CalamityCow/MacOS-Keyboard-Submission/PCB/LED.kicad_sch

## KiCad design PCB/LED.kicad_sch (2025-12-03)

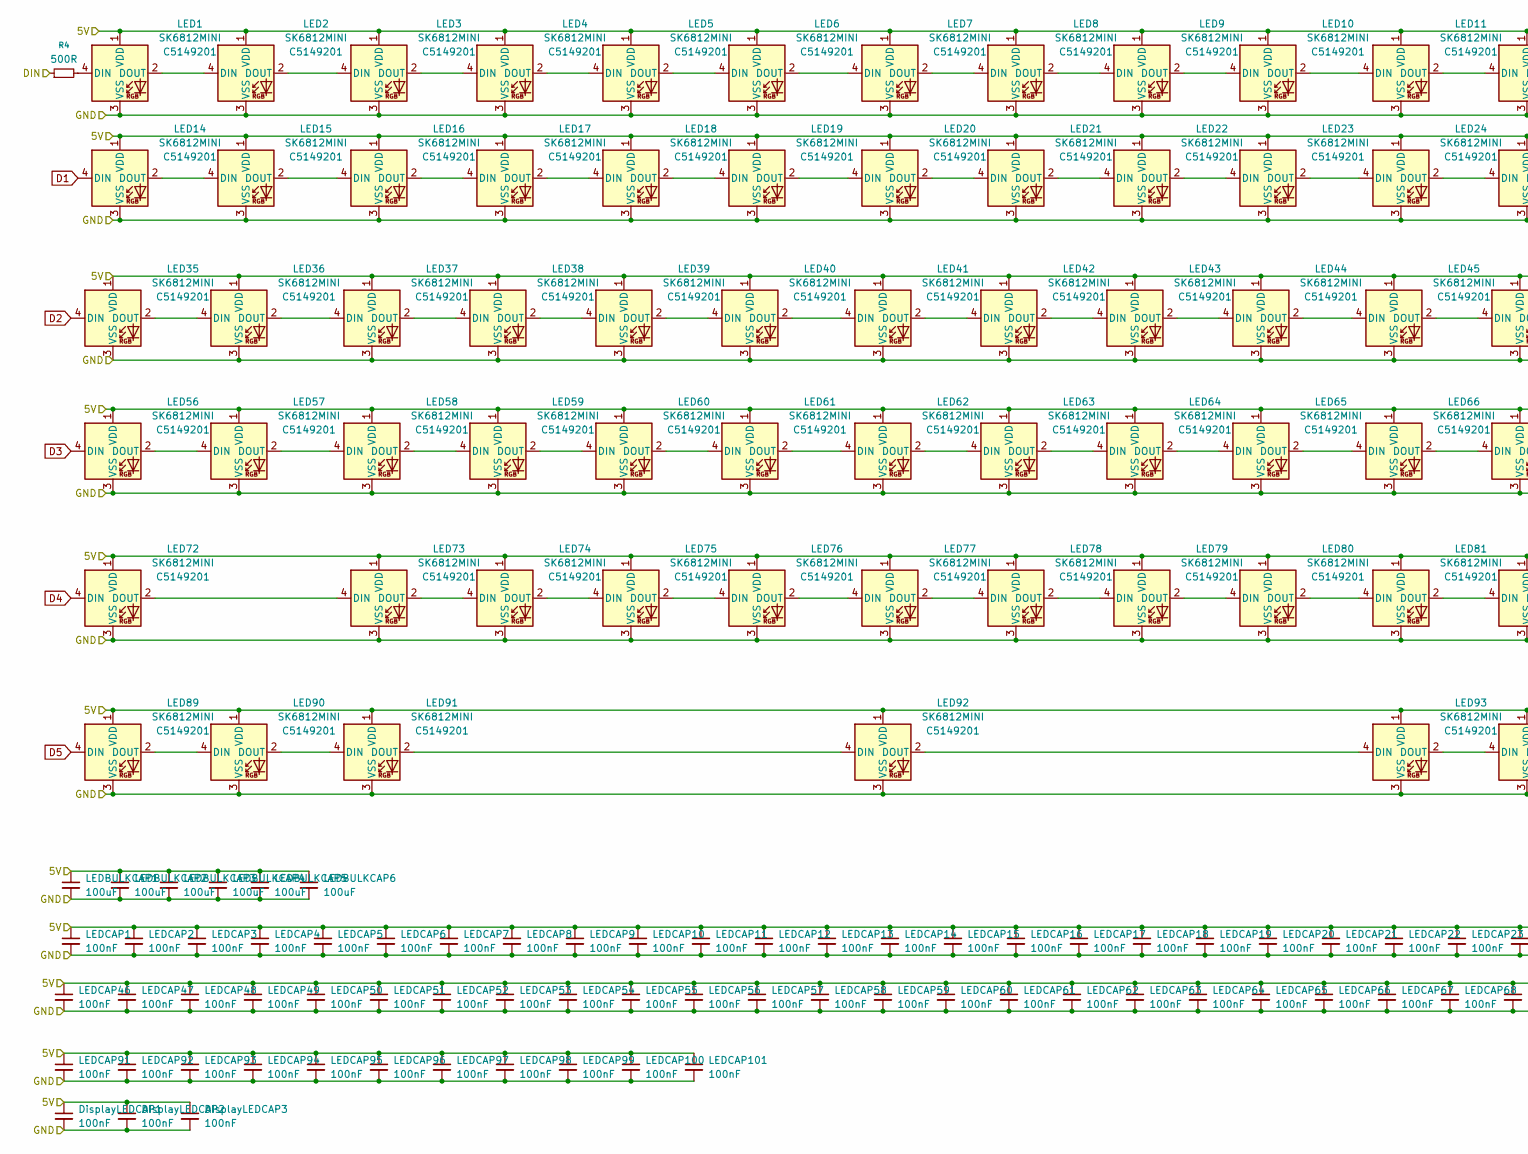
[picture p2: schematic LED.kicad_sch, part in row 1, column 1]

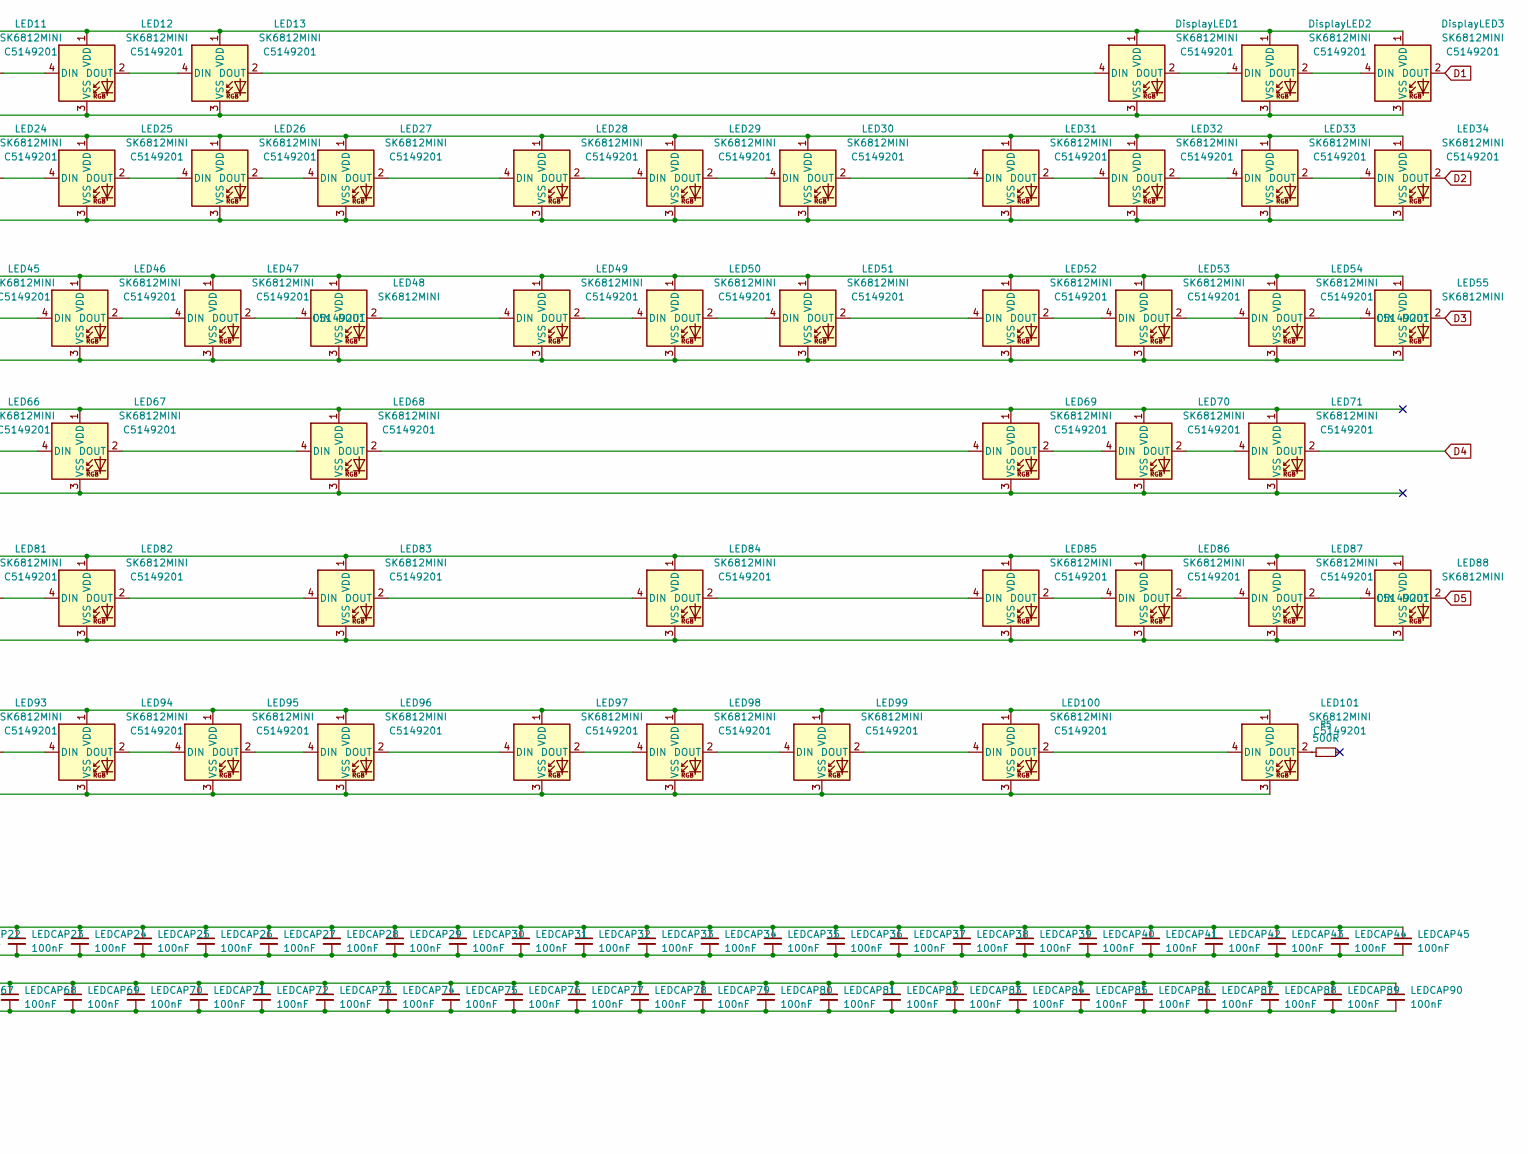
[picture p3: schematic LED.kicad_sch, part in row 1, column 2]

Parts:
DisplayLED1, DisplayLED2, DisplayLED3: SK6812MINI; LED_SK6812MINI; LCSC C5149201
DisplayLEDCAP1, DisplayLEDCAP2, DisplayLEDCAP3: 100nF; Capacitor_0402
LED1, LED2, LED3, LED4, LED5, LED6, LED7, LED8, LED9, LED10, LED11, LED12, LED13, LED14, LED15, LED16, LED17, LED18, LED19, LED20, LED21, LED22, LED23, LED24, LED25, LED26, LED27, LED28, LED29, LED30, LED31, LED32, LED33, LED34, LED35, LED36, LED37, LED38, LED39, LED40, LED41, LED42, LED43, LED44, LED45, LED46, LED47, LED48, LED49, LED50, LED51, LED52, LED53, LED54, LED55, LED56, LED57, LED58, LED59, LED60, LED61, LED62, LED63, LED64, LED65, LED66, LED67, LED68, LED69, LED70, LED71, LED72, LED73, LED74, LED75, LED76, LED77, LED78, LED79, LED80, LED81, LED82, LED83, LED84, LED85, LED86, LED87, LED88, LED89, LED90, LED91, LED92, LED93, LED94, LED95, LED96, LED97, LED98, LED99, LED100, LED101: SK6812MINI; LED_SK6812MINI; LCSC C5149201
LEDBULKCAP1, LEDBULKCAP2, LEDBULKCAP3, LEDBULKCAP4, LEDBULKCAP5, LEDBULKCAP6: 100uF; Capacitor_0402
LEDCAP1, LEDCAP2, LEDCAP3, LEDCAP4, LEDCAP5, LEDCAP6, LEDCAP7, LEDCAP8, LEDCAP9, LEDCAP10, LEDCAP11, LEDCAP12, LEDCAP13, LEDCAP14, LEDCAP15, LEDCAP16, LEDCAP17, LEDCAP18, LEDCAP19, LEDCAP20, LEDCAP21, LEDCAP22, LEDCAP23, LEDCAP24, LEDCAP25, LEDCAP26, LEDCAP27, LEDCAP28, LEDCAP29, LEDCAP30, LEDCAP31, LEDCAP32, LEDCAP33, LEDCAP34, LEDCAP35, LEDCAP36, LEDCAP37, LEDCAP38, LEDCAP39, LEDCAP40, LEDCAP41, LEDCAP42, LEDCAP43, LEDCAP44, LEDCAP45, LEDCAP46, LEDCAP47, LEDCAP48, LEDCAP49, LEDCAP50, LEDCAP51, LEDCAP52, LEDCAP53, LEDCAP54, LEDCAP55, LEDCAP56, LEDCAP57, LEDCAP58, LEDCAP59, LEDCAP60, LEDCAP61, LEDCAP62, LEDCAP63, LEDCAP64, LEDCAP65, LEDCAP66, LEDCAP67, LEDCAP68, LEDCAP69, LEDCAP70, LEDCAP71, LEDCAP72, LEDCAP73, LEDCAP74, LEDCAP75, LEDCAP76, LEDCAP77, LEDCAP78, LEDCAP79, LEDCAP80, LEDCAP81, LEDCAP82, LEDCAP83, LEDCAP84, LEDCAP85, LEDCAP86, LEDCAP87, LEDCAP88, LEDCAP89, LEDCAP90, LEDCAP91, LEDCAP92, LEDCAP93, LEDCAP94, LEDCAP95, LEDCAP96, LEDCAP97, LEDCAP98, LEDCAP99, LEDCAP100, LEDCAP101: 100nF; Capacitor_0402
R4, R5: 500R; Resistor_0402

Connections:
5V: DisplayLED1.1 (VDD), DisplayLED2.1 (VDD), DisplayLED3.1 (VDD), DisplayLEDCAP1.1, DisplayLEDCAP2.1, DisplayLEDCAP3.1, LED1.1 (VDD), LED2.1 (VDD), LED3.1 (VDD), LED4.1 (VDD), LED5.1 (VDD), LED6.1 (VDD), LED7.1 (VDD), LED8.1 (VDD), LED9.1 (VDD), LED10.1 (VDD), LED11.1 (VDD), LED12.1 (VDD), LED13.1 (VDD), LED14.1 (VDD), LED15.1 (VDD), LED16.1 (VDD), LED17.1 (VDD), LED18.1 (VDD), LED19.1 (VDD), LED20.1 (VDD), LED21.1 (VDD), LED22.1 (VDD), LED23.1 (VDD), LED24.1 (VDD), LED25.1 (VDD), LED26.1 (VDD), LED27.1 (VDD), LED28.1 (VDD), LED29.1 (VDD), LED30.1 (VDD), LED31.1 (VDD), LED32.1 (VDD), LED33.1 (VDD), LED34.1 (VDD), LED35.1 (VDD), LED36.1 (VDD), LED37.1 (VDD), LED38.1 (VDD), LED39.1 (VDD), LED40.1 (VDD), LED41.1 (VDD), LED42.1 (VDD), LED43.1 (VDD), LED44.1 (VDD), LED45.1 (VDD), LED46.1 (VDD), LED47.1 (VDD), LED48.1 (VDD), LED49.1 (VDD), LED50.1 (VDD), LED51.1 (VDD), LED52.1 (VDD), LED53.1 (VDD), LED54.1 (VDD), LED55.1 (VDD), LED56.1 (VDD), LED57.1 (VDD), LED58.1 (VDD), LED59.1 (VDD), LED60.1 (VDD), LED61.1 (VDD), LED62.1 (VDD), LED63.1 (VDD), LED64.1 (VDD), LED65.1 (VDD), LED66.1 (VDD), LED67.1 (VDD), LED68.1 (VDD), LED69.1 (VDD), LED70.1 (VDD), LED71.1 (VDD), LED72.1 (VDD), LED73.1 (VDD), LED74.1 (VDD), LED75.1 (VDD), LED76.1 (VDD), LED77.1 (VDD), LED78.1 (VDD), LED79.1 (VDD), LED80.1 (VDD), LED81.1 (VDD), LED82.1 (VDD), LED83.1 (VDD), LED84.1 (VDD), LED85.1 (VDD), LED86.1 (VDD), LED87.1 (VDD), LED88.1 (VDD), LED89.1 (VDD), LED90.1 (VDD), LED91.1 (VDD), LED92.1 (VDD), LED93.1 (VDD), LED94.1 (VDD), LED95.1 (VDD), LED96.1 (VDD), LED97.1 (VDD), LED98.1 (VDD), LED99.1 (VDD), LED100.1 (VDD), LED101.1 (VDD), LEDBULKCAP1.1, LEDBULKCAP2.1, LEDBULKCAP3.1, LEDBULKCAP4.1, LEDBULKCAP5.1, LEDBULKCAP6.1, LEDCAP1.1, LEDCAP2.1, LEDCAP3.1, LEDCAP4.1, LEDCAP5.1, LEDCAP6.1, LEDCAP7.1, LEDCAP8.1, LEDCAP9.1, LEDCAP10.1, LEDCAP11.1, LEDCAP12.1, LEDCAP13.1, LEDCAP14.1, LEDCAP15.1, LEDCAP16.1, LEDCAP17.1, LEDCAP18.1, LEDCAP19.1, LEDCAP20.1, LEDCAP21.1, LEDCAP22.1, LEDCAP23.1, LEDCAP24.1, LEDCAP25.1, LEDCAP26.1, LEDCAP27.1, LEDCAP28.1, LEDCAP29.1, LEDCAP30.1, LEDCAP31.1, LEDCAP32.1, LEDCAP33.1, LEDCAP34.1, LEDCAP35.1, LEDCAP36.1, LEDCAP37.1, LEDCAP38.1, LEDCAP39.1, LEDCAP40.1, LEDCAP41.1, LEDCAP42.1, LEDCAP43.1, LEDCAP44.1, LEDCAP45.1, LEDCAP46.1, LEDCAP47.1, LEDCAP48.1, LEDCAP49.1, LEDCAP50.1, LEDCAP51.1, LEDCAP52.1, LEDCAP53.1, LEDCAP54.1, LEDCAP55.1, LEDCAP56.1, LEDCAP57.1, LEDCAP58.1, LEDCAP59.1, LEDCAP60.1, LEDCAP61.1, LEDCAP62.1, LEDCAP63.1, LEDCAP64.1, LEDCAP65.1, LEDCAP66.1, LEDCAP67.1, LEDCAP68.1, LEDCAP69.1, LEDCAP70.1, LEDCAP71.1, LEDCAP72.1, LEDCAP73.1, LEDCAP74.1, LEDCAP75.1, LEDCAP76.1, LEDCAP77.1, LEDCAP78.1, LEDCAP79.1, LEDCAP80.1, LEDCAP81.1, LEDCAP82.1, LEDCAP83.1, LEDCAP84.1, LEDCAP85.1, LEDCAP86.1, LEDCAP87.1, LEDCAP88.1, LEDCAP89.1, LEDCAP90.1, LEDCAP91.1, LEDCAP92.1, LEDCAP93.1, LEDCAP94.1, LEDCAP95.1, LEDCAP96.1, LEDCAP97.1, LEDCAP98.1, LEDCAP99.1, LEDCAP100.1, LEDCAP101.1
D1: DisplayLED3.2 (DOUT), LED14.4 (DIN)
D2: LED34.2 (DOUT), LED35.4 (DIN)
D3: LED55.2 (DOUT), LED56.4 (DIN)
D4: LED71.2 (DOUT), LED72.4 (DIN)
D5: LED88.2 (DOUT), LED89.4 (DIN)
DIN: R4.1
GND: DisplayLED1.3 (VSS), DisplayLED2.3 (VSS), DisplayLED3.3 (VSS), DisplayLEDCAP1.2, DisplayLEDCAP2.2, DisplayLEDCAP3.2, LED1.3 (VSS), LED2.3 (VSS), LED3.3 (VSS), LED4.3 (VSS), LED5.3 (VSS), LED6.3 (VSS), LED7.3 (VSS), LED8.3 (VSS), LED9.3 (VSS), LED10.3 (VSS), LED11.3 (VSS), LED12.3 (VSS), LED13.3 (VSS), LED14.3 (VSS), LED15.3 (VSS), LED16.3 (VSS), LED17.3 (VSS), LED18.3 (VSS), LED19.3 (VSS), LED20.3 (VSS), LED21.3 (VSS), LED22.3 (VSS), LED23.3 (VSS), LED24.3 (VSS), LED25.3 (VSS), LED26.3 (VSS), LED27.3 (VSS), LED28.3 (VSS), LED29.3 (VSS), LED30.3 (VSS), LED31.3 (VSS), LED32.3 (VSS), LED33.3 (VSS), LED34.3 (VSS), LED35.3 (VSS), LED36.3 (VSS), LED37.3 (VSS), LED38.3 (VSS), LED39.3 (VSS), LED40.3 (VSS), LED41.3 (VSS), LED42.3 (VSS), LED43.3 (VSS), LED44.3 (VSS), LED45.3 (VSS), LED46.3 (VSS), LED47.3 (VSS), LED48.3 (VSS), LED49.3 (VSS), LED50.3 (VSS), LED51.3 (VSS), LED52.3 (VSS), LED53.3 (VSS), LED54.3 (VSS), LED55.3 (VSS), LED56.3 (VSS), LED57.3 (VSS), LED58.3 (VSS), LED59.3 (VSS), LED60.3 (VSS), LED61.3 (VSS), LED62.3 (VSS), LED63.3 (VSS), LED64.3 (VSS), LED65.3 (VSS), LED66.3 (VSS), LED67.3 (VSS), LED68.3 (VSS), LED69.3 (VSS), LED70.3 (VSS), LED71.3 (VSS), LED72.3 (VSS), LED73.3 (VSS), LED74.3 (VSS), LED75.3 (VSS), LED76.3 (VSS), LED77.3 (VSS), LED78.3 (VSS), LED79.3 (VSS), LED80.3 (VSS), LED81.3 (VSS), LED82.3 (VSS), LED83.3 (VSS), LED84.3 (VSS), LED85.3 (VSS), LED86.3 (VSS), LED87.3 (VSS), LED88.3 (VSS), LED89.3 (VSS), LED90.3 (VSS), LED91.3 (VSS), LED92.3 (VSS), LED93.3 (VSS), LED94.3 (VSS), LED95.3 (VSS), LED96.3 (VSS), LED97.3 (VSS), LED98.3 (VSS), LED99.3 (VSS), LED100.3 (VSS), LED101.3 (VSS), LEDBULKCAP1.2, LEDBULKCAP2.2, LEDBULKCAP3.2, LEDBULKCAP4.2, LEDBULKCAP5.2, LEDBULKCAP6.2, LEDCAP1.2, LEDCAP2.2, LEDCAP3.2, LEDCAP4.2, LEDCAP5.2, LEDCAP6.2, LEDCAP7.2, LEDCAP8.2, LEDCAP9.2, LEDCAP10.2, LEDCAP11.2, LEDCAP12.2, LEDCAP13.2, LEDCAP14.2, LEDCAP15.2, LEDCAP16.2, LEDCAP17.2, LEDCAP18.2, LEDCAP19.2, LEDCAP20.2, LEDCAP21.2, LEDCAP22.2, LEDCAP23.2, LEDCAP24.2, LEDCAP25.2, LEDCAP26.2, LEDCAP27.2, LEDCAP28.2, LEDCAP29.2, LEDCAP30.2, LEDCAP31.2, LEDCAP32.2, LEDCAP33.2, LEDCAP34.2, LEDCAP35.2, LEDCAP36.2, LEDCAP37.2, LEDCAP38.2, LEDCAP39.2, LEDCAP40.2, LEDCAP41.2, LEDCAP42.2, LEDCAP43.2, LEDCAP44.2, LEDCAP45.2, LEDCAP46.2, LEDCAP47.2, LEDCAP48.2, LEDCAP49.2, LEDCAP50.2, LEDCAP51.2, LEDCAP52.2, LEDCAP53.2, LEDCAP54.2, LEDCAP55.2, LEDCAP56.2, LEDCAP57.2, LEDCAP58.2, LEDCAP59.2, LEDCAP60.2, LEDCAP61.2, LEDCAP62.2, LEDCAP63.2, LEDCAP64.2, LEDCAP65.2, LEDCAP66.2, LEDCAP67.2, LEDCAP68.2, LEDCAP69.2, LEDCAP70.2, LEDCAP71.2, LEDCAP72.2, LEDCAP73.2, LEDCAP74.2, LEDCAP75.2, LEDCAP76.2, LEDCAP77.2, LEDCAP78.2, LEDCAP79.2, LEDCAP80.2, LEDCAP81.2, LEDCAP82.2, LEDCAP83.2, LEDCAP84.2, LEDCAP85.2, LEDCAP86.2, LEDCAP87.2, LEDCAP88.2, LEDCAP89.2, LEDCAP90.2, LEDCAP91.2, LEDCAP92.2, LEDCAP93.2, LEDCAP94.2, LEDCAP95.2, LEDCAP96.2, LEDCAP97.2, LEDCAP98.2, LEDCAP99.2, LEDCAP100.2, LEDCAP101.2
unnamed: DisplayLED1.2 (DOUT), DisplayLED2.4 (DIN)
unnamed: DisplayLED1.4 (DIN), LED13.2 (DOUT)
unnamed: DisplayLED2.2 (DOUT), DisplayLED3.4 (DIN)
unnamed: LED1.2 (DOUT), LED2.4 (DIN)
unnamed: LED1.4 (DIN), R4.2
unnamed: LED2.2 (DOUT), LED3.4 (DIN)
unnamed: LED3.2 (DOUT), LED4.4 (DIN)
unnamed: LED4.2 (DOUT), LED5.4 (DIN)
unnamed: LED5.2 (DOUT), LED6.4 (DIN)
unnamed: LED6.2 (DOUT), LED7.4 (DIN)
unnamed: LED7.2 (DOUT), LED8.4 (DIN)
unnamed: LED8.2 (DOUT), LED9.4 (DIN)
unnamed: LED10.2 (DOUT), LED11.4 (DIN)
unnamed: LED9.2 (DOUT), LED10.4 (DIN)
unnamed: LED11.2 (DOUT), LED12.4 (DIN)
unnamed: LED12.2 (DOUT), LED13.4 (DIN)
unnamed: LED14.2 (DOUT), LED15.4 (DIN)
unnamed: LED15.2 (DOUT), LED16.4 (DIN)
unnamed: LED16.2 (DOUT), LED17.4 (DIN)
unnamed: LED17.2 (DOUT), LED18.4 (DIN)
unnamed: LED18.2 (DOUT), LED19.4 (DIN)
unnamed: LED19.2 (DOUT), LED20.4 (DIN)
unnamed: LED20.2 (DOUT), LED21.4 (DIN)
unnamed: LED21.2 (DOUT), LED22.4 (DIN)
unnamed: LED22.2 (DOUT), LED23.4 (DIN)
unnamed: LED23.2 (DOUT), LED24.4 (DIN)
unnamed: LED24.2 (DOUT), LED25.4 (DIN)
unnamed: LED25.2 (DOUT), LED26.4 (DIN)
unnamed: LED26.2 (DOUT), LED27.4 (DIN)
unnamed: LED27.2 (DOUT), LED28.4 (DIN)
unnamed: LED28.2 (DOUT), LED29.4 (DIN)
unnamed: LED29.2 (DOUT), LED30.4 (DIN)
unnamed: LED30.2 (DOUT), LED31.4 (DIN)
unnamed: LED31.2 (DOUT), LED32.4 (DIN)
unnamed: LED32.2 (DOUT), LED33.4 (DIN)
unnamed: LED33.2 (DOUT), LED34.4 (DIN)
unnamed: LED35.2 (DOUT), LED36.4 (DIN)
unnamed: LED36.2 (DOUT), LED37.4 (DIN)
unnamed: LED37.2 (DOUT), LED38.4 (DIN)
unnamed: LED38.2 (DOUT), LED39.4 (DIN)
unnamed: LED39.2 (DOUT), LED40.4 (DIN)
unnamed: LED40.2 (DOUT), LED41.4 (DIN)
unnamed: LED41.2 (DOUT), LED42.4 (DIN)
unnamed: LED42.2 (DOUT), LED43.4 (DIN)
unnamed: LED43.2 (DOUT), LED44.4 (DIN)
unnamed: LED44.2 (DOUT), LED45.4 (DIN)
unnamed: LED45.2 (DOUT), LED46.4 (DIN)
unnamed: LED46.2 (DOUT), LED47.4 (DIN)
unnamed: LED47.2 (DOUT), LED48.4 (DIN)
unnamed: LED48.2 (DOUT), LED49.4 (DIN)
unnamed: LED49.2 (DOUT), LED50.4 (DIN)
unnamed: LED50.2 (DOUT), LED51.4 (DIN)
unnamed: LED51.2 (DOUT), LED52.4 (DIN)
unnamed: LED52.2 (DOUT), LED53.4 (DIN)
unnamed: LED53.2 (DOUT), LED54.4 (DIN)
unnamed: LED54.2 (DOUT), LED55.4 (DIN)
unnamed: LED56.2 (DOUT), LED57.4 (DIN)
unnamed: LED57.2 (DOUT), LED58.4 (DIN)
unnamed: LED58.2 (DOUT), LED59.4 (DIN)
unnamed: LED59.2 (DOUT), LED60.4 (DIN)
unnamed: LED60.2 (DOUT), LED61.4 (DIN)
unnamed: LED61.2 (DOUT), LED62.4 (DIN)
unnamed: LED62.2 (DOUT), LED63.4 (DIN)
unnamed: LED63.2 (DOUT), LED64.4 (DIN)
unnamed: LED64.2 (DOUT), LED65.4 (DIN)
unnamed: LED65.2 (DOUT), LED66.4 (DIN)
unnamed: LED66.2 (DOUT), LED67.4 (DIN)
unnamed: LED67.2 (DOUT), LED68.4 (DIN)
unnamed: LED68.2 (DOUT), LED69.4 (DIN)
unnamed: LED69.2 (DOUT), LED70.4 (DIN)
unnamed: LED70.2 (DOUT), LED71.4 (DIN)
unnamed: LED72.2 (DOUT), LED73.4 (DIN)
unnamed: LED73.2 (DOUT), LED74.4 (DIN)
unnamed: LED74.2 (DOUT), LED75.4 (DIN)
unnamed: LED75.2 (DOUT), LED76.4 (DIN)
unnamed: LED76.2 (DOUT), LED77.4 (DIN)
unnamed: LED77.2 (DOUT), LED78.4 (DIN)
unnamed: LED78.2 (DOUT), LED79.4 (DIN)
unnamed: LED79.2 (DOUT), LED80.4 (DIN)
unnamed: LED80.2 (DOUT), LED81.4 (DIN)
unnamed: LED81.2 (DOUT), LED82.4 (DIN)
unnamed: LED82.2 (DOUT), LED83.4 (DIN)
unnamed: LED83.2 (DOUT), LED84.4 (DIN)
unnamed: LED84.2 (DOUT), LED85.4 (DIN)
unnamed: LED85.2 (DOUT), LED86.4 (DIN)
unnamed: LED86.2 (DOUT), LED87.4 (DIN)
unnamed: LED87.2 (DOUT), LED88.4 (DIN)
unnamed: LED89.2 (DOUT), LED90.4 (DIN)
unnamed: LED90.2 (DOUT), LED91.4 (DIN)
unnamed: LED91.2 (DOUT), LED92.4 (DIN)
unnamed: LED92.2 (DOUT), LED93.4 (DIN)
unnamed: LED93.2 (DOUT), LED94.4 (DIN)
unnamed: LED94.2 (DOUT), LED95.4 (DIN)
unnamed: LED95.2 (DOUT), LED96.4 (DIN)
unnamed: LED96.2 (DOUT), LED97.4 (DIN)
unnamed: LED97.2 (DOUT), LED98.4 (DIN)
unnamed: LED98.2 (DOUT), LED99.4 (DIN)
unnamed: LED100.2 (DOUT), LED101.4 (DIN)
unnamed: LED99.2 (DOUT), LED100.4 (DIN)
unnamed: LED101.2 (DOUT), R5.1
