CalamityCow/MacOS-Keyboard-Submission/PCB/ScottoModules.kicad_sch

## KiCad design PCB/ScottoModules.kicad_sch (2025-12-03)

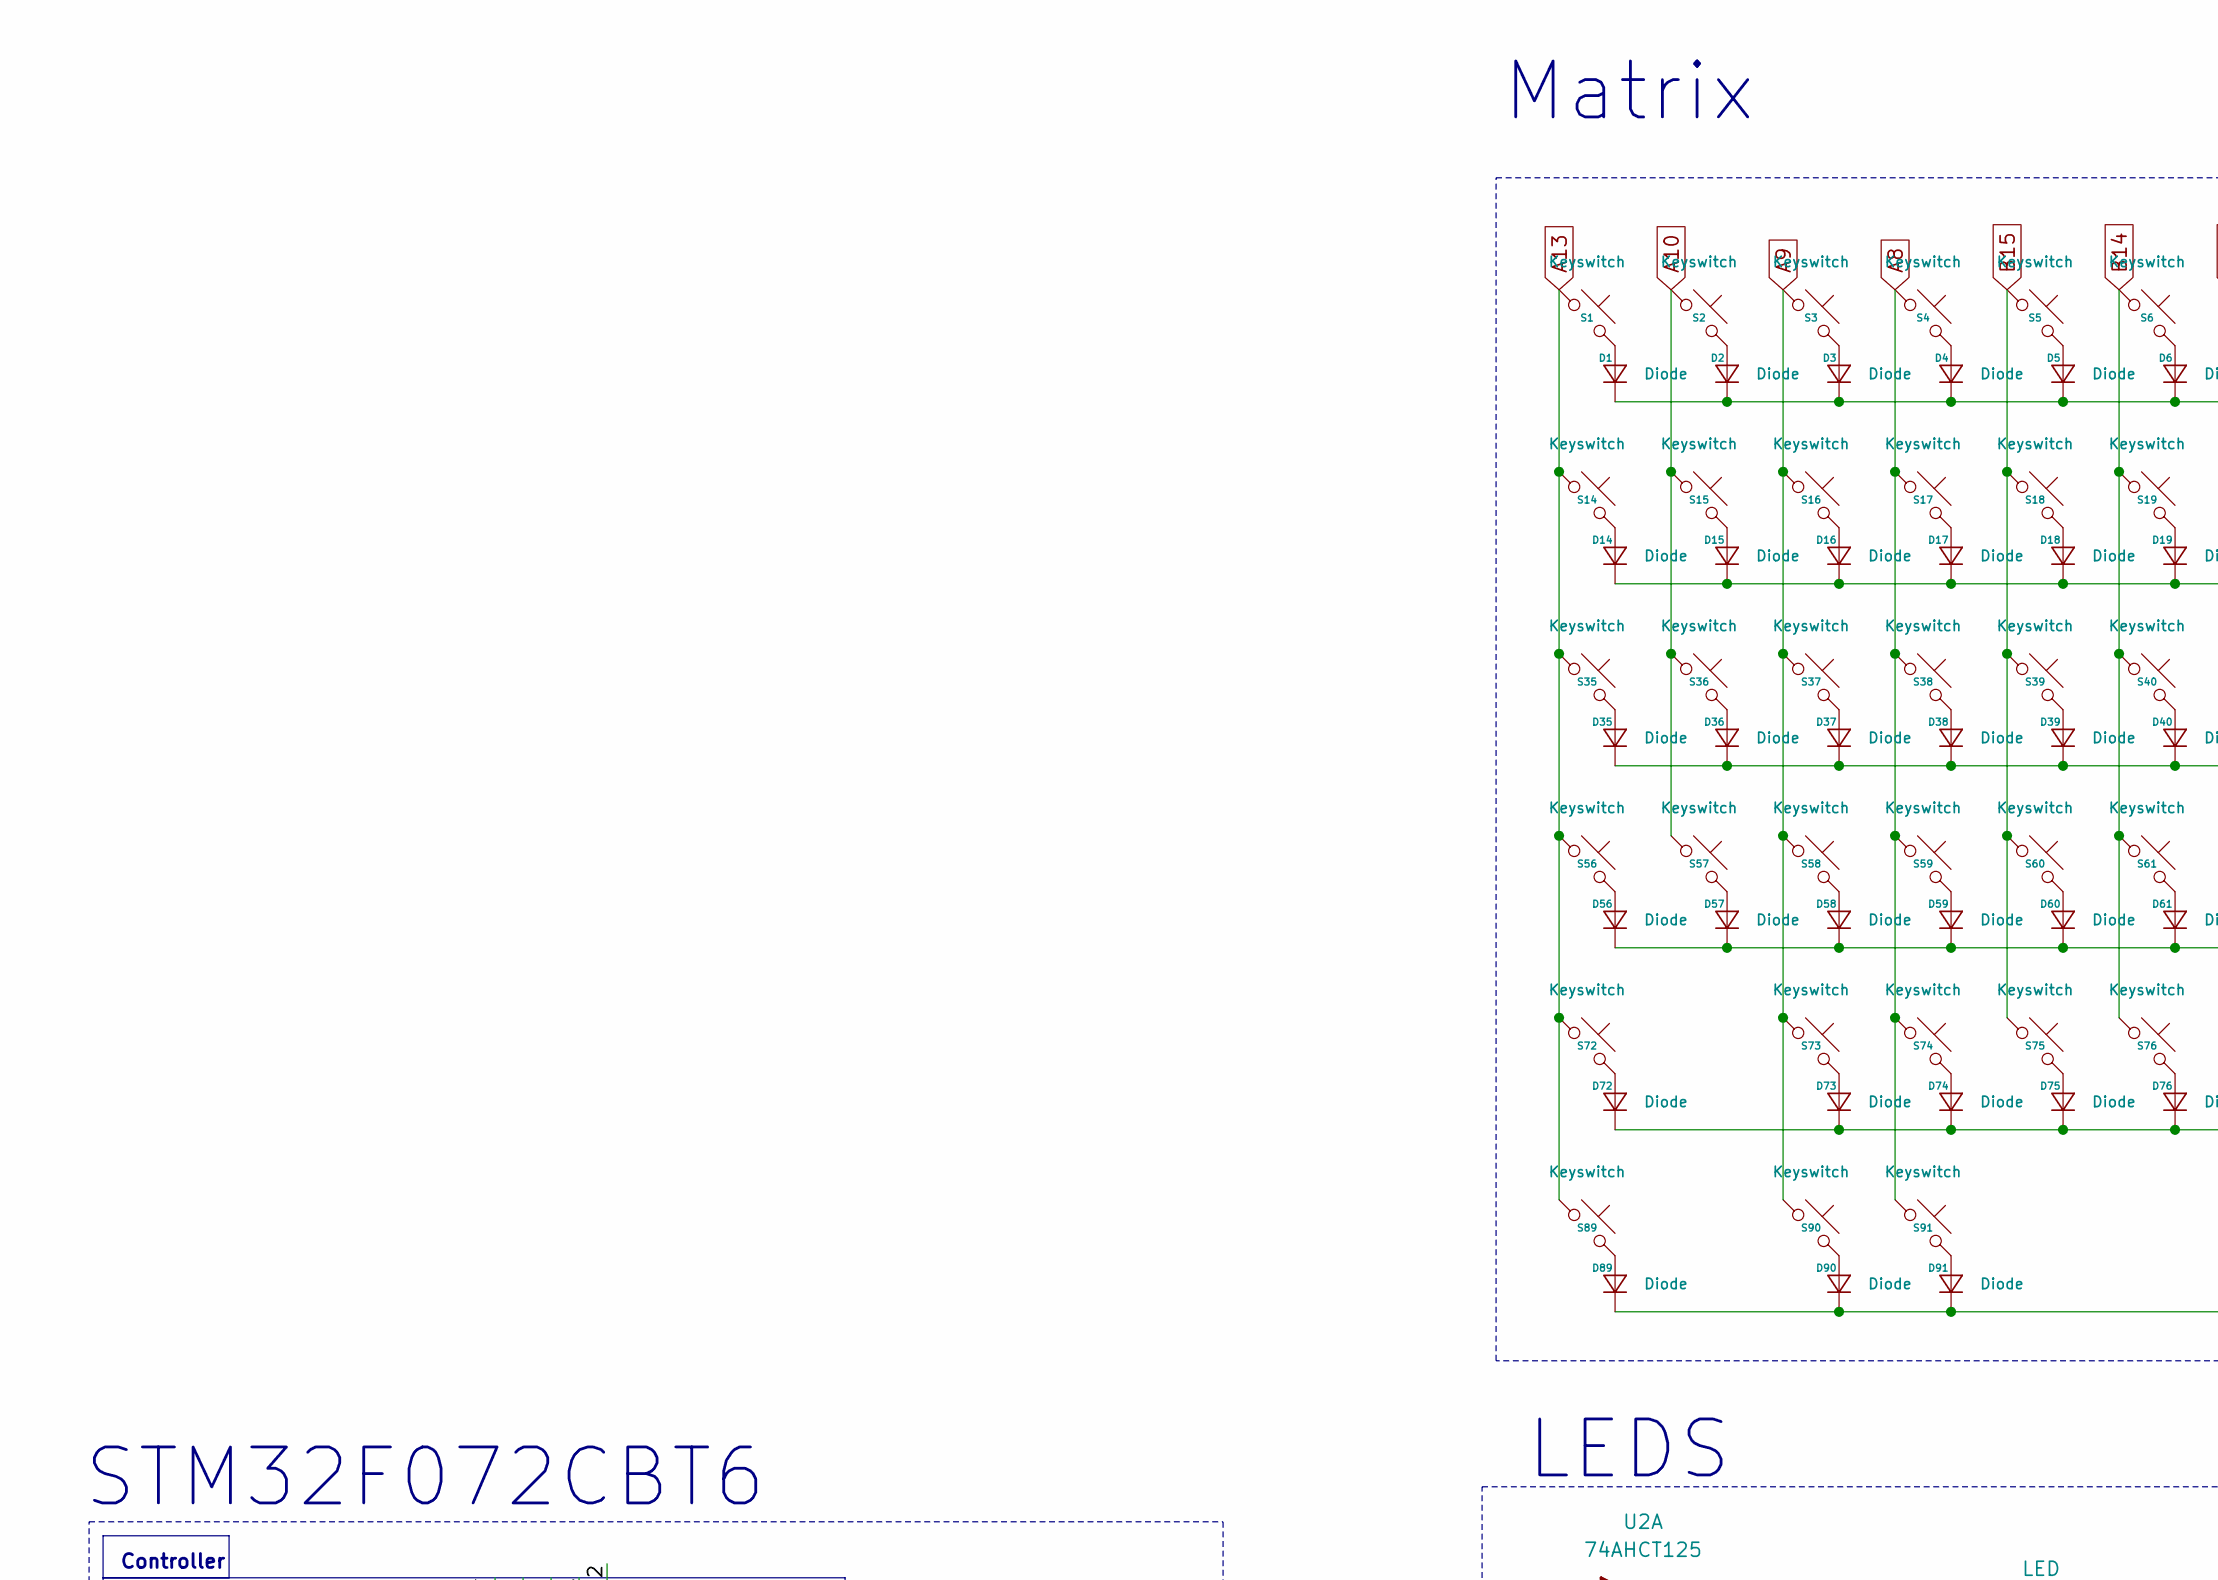
[picture p4: schematic ScottoModules.kicad_sch, part in row 1, column 1]

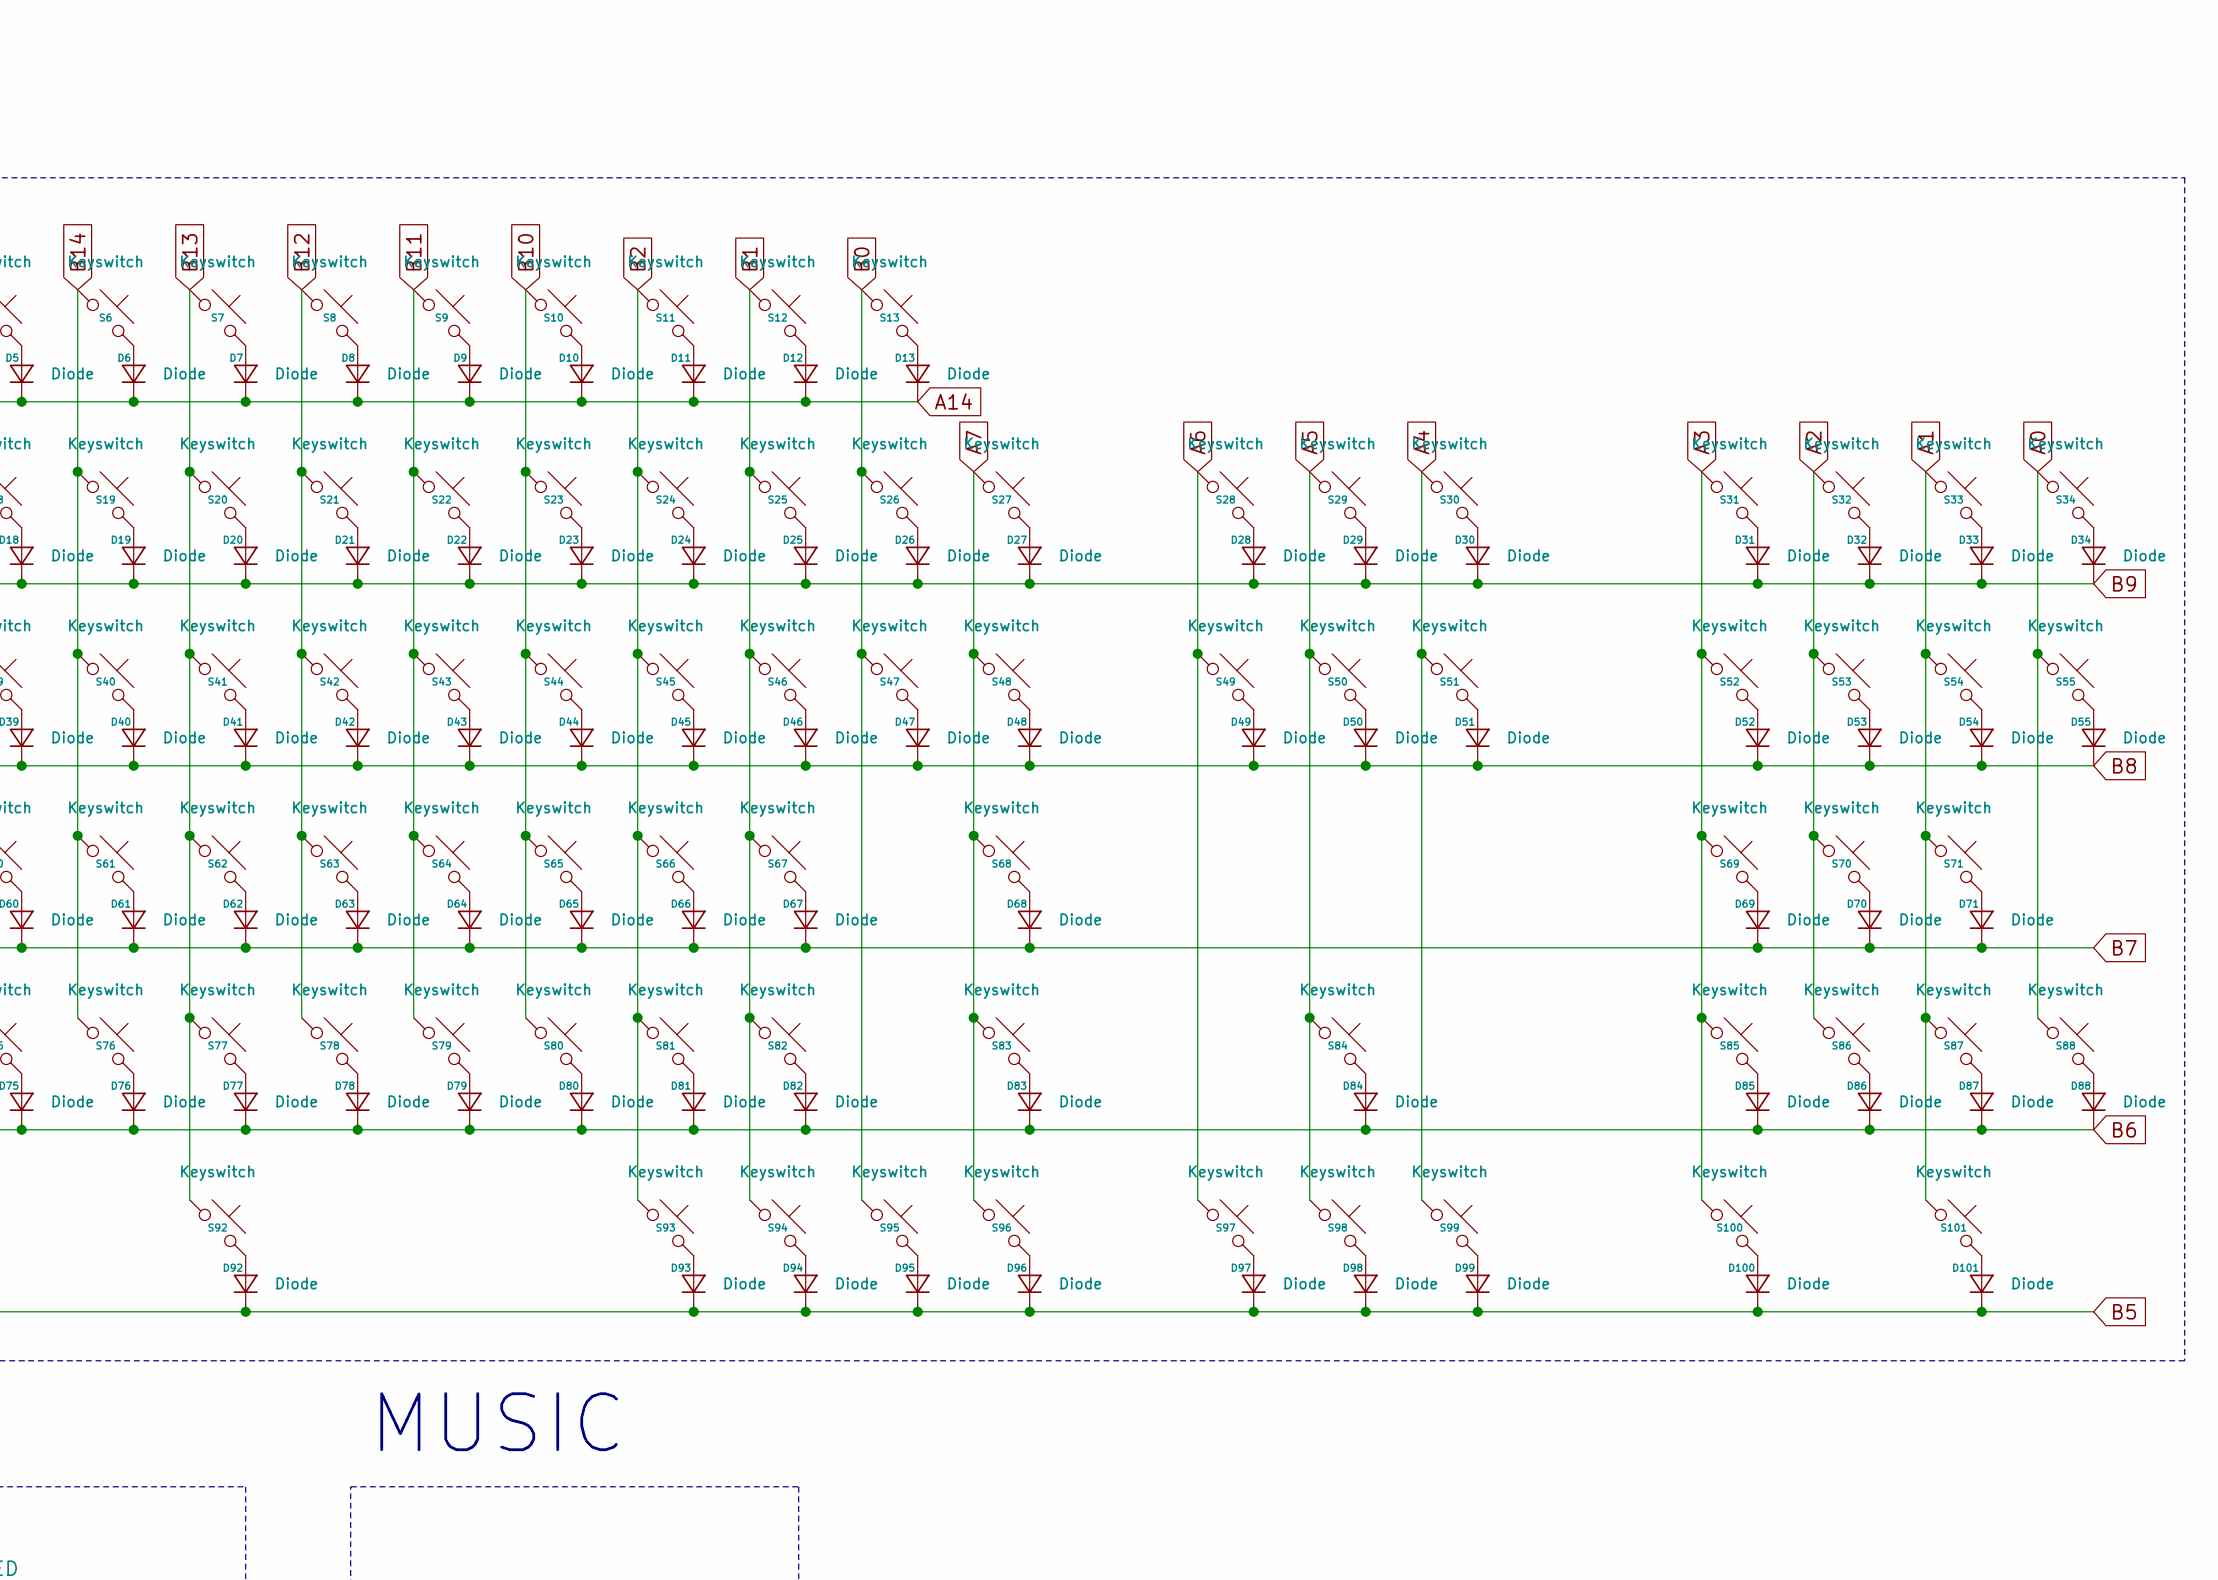
[picture p5: schematic ScottoModules.kicad_sch, part in row 1, column 2]

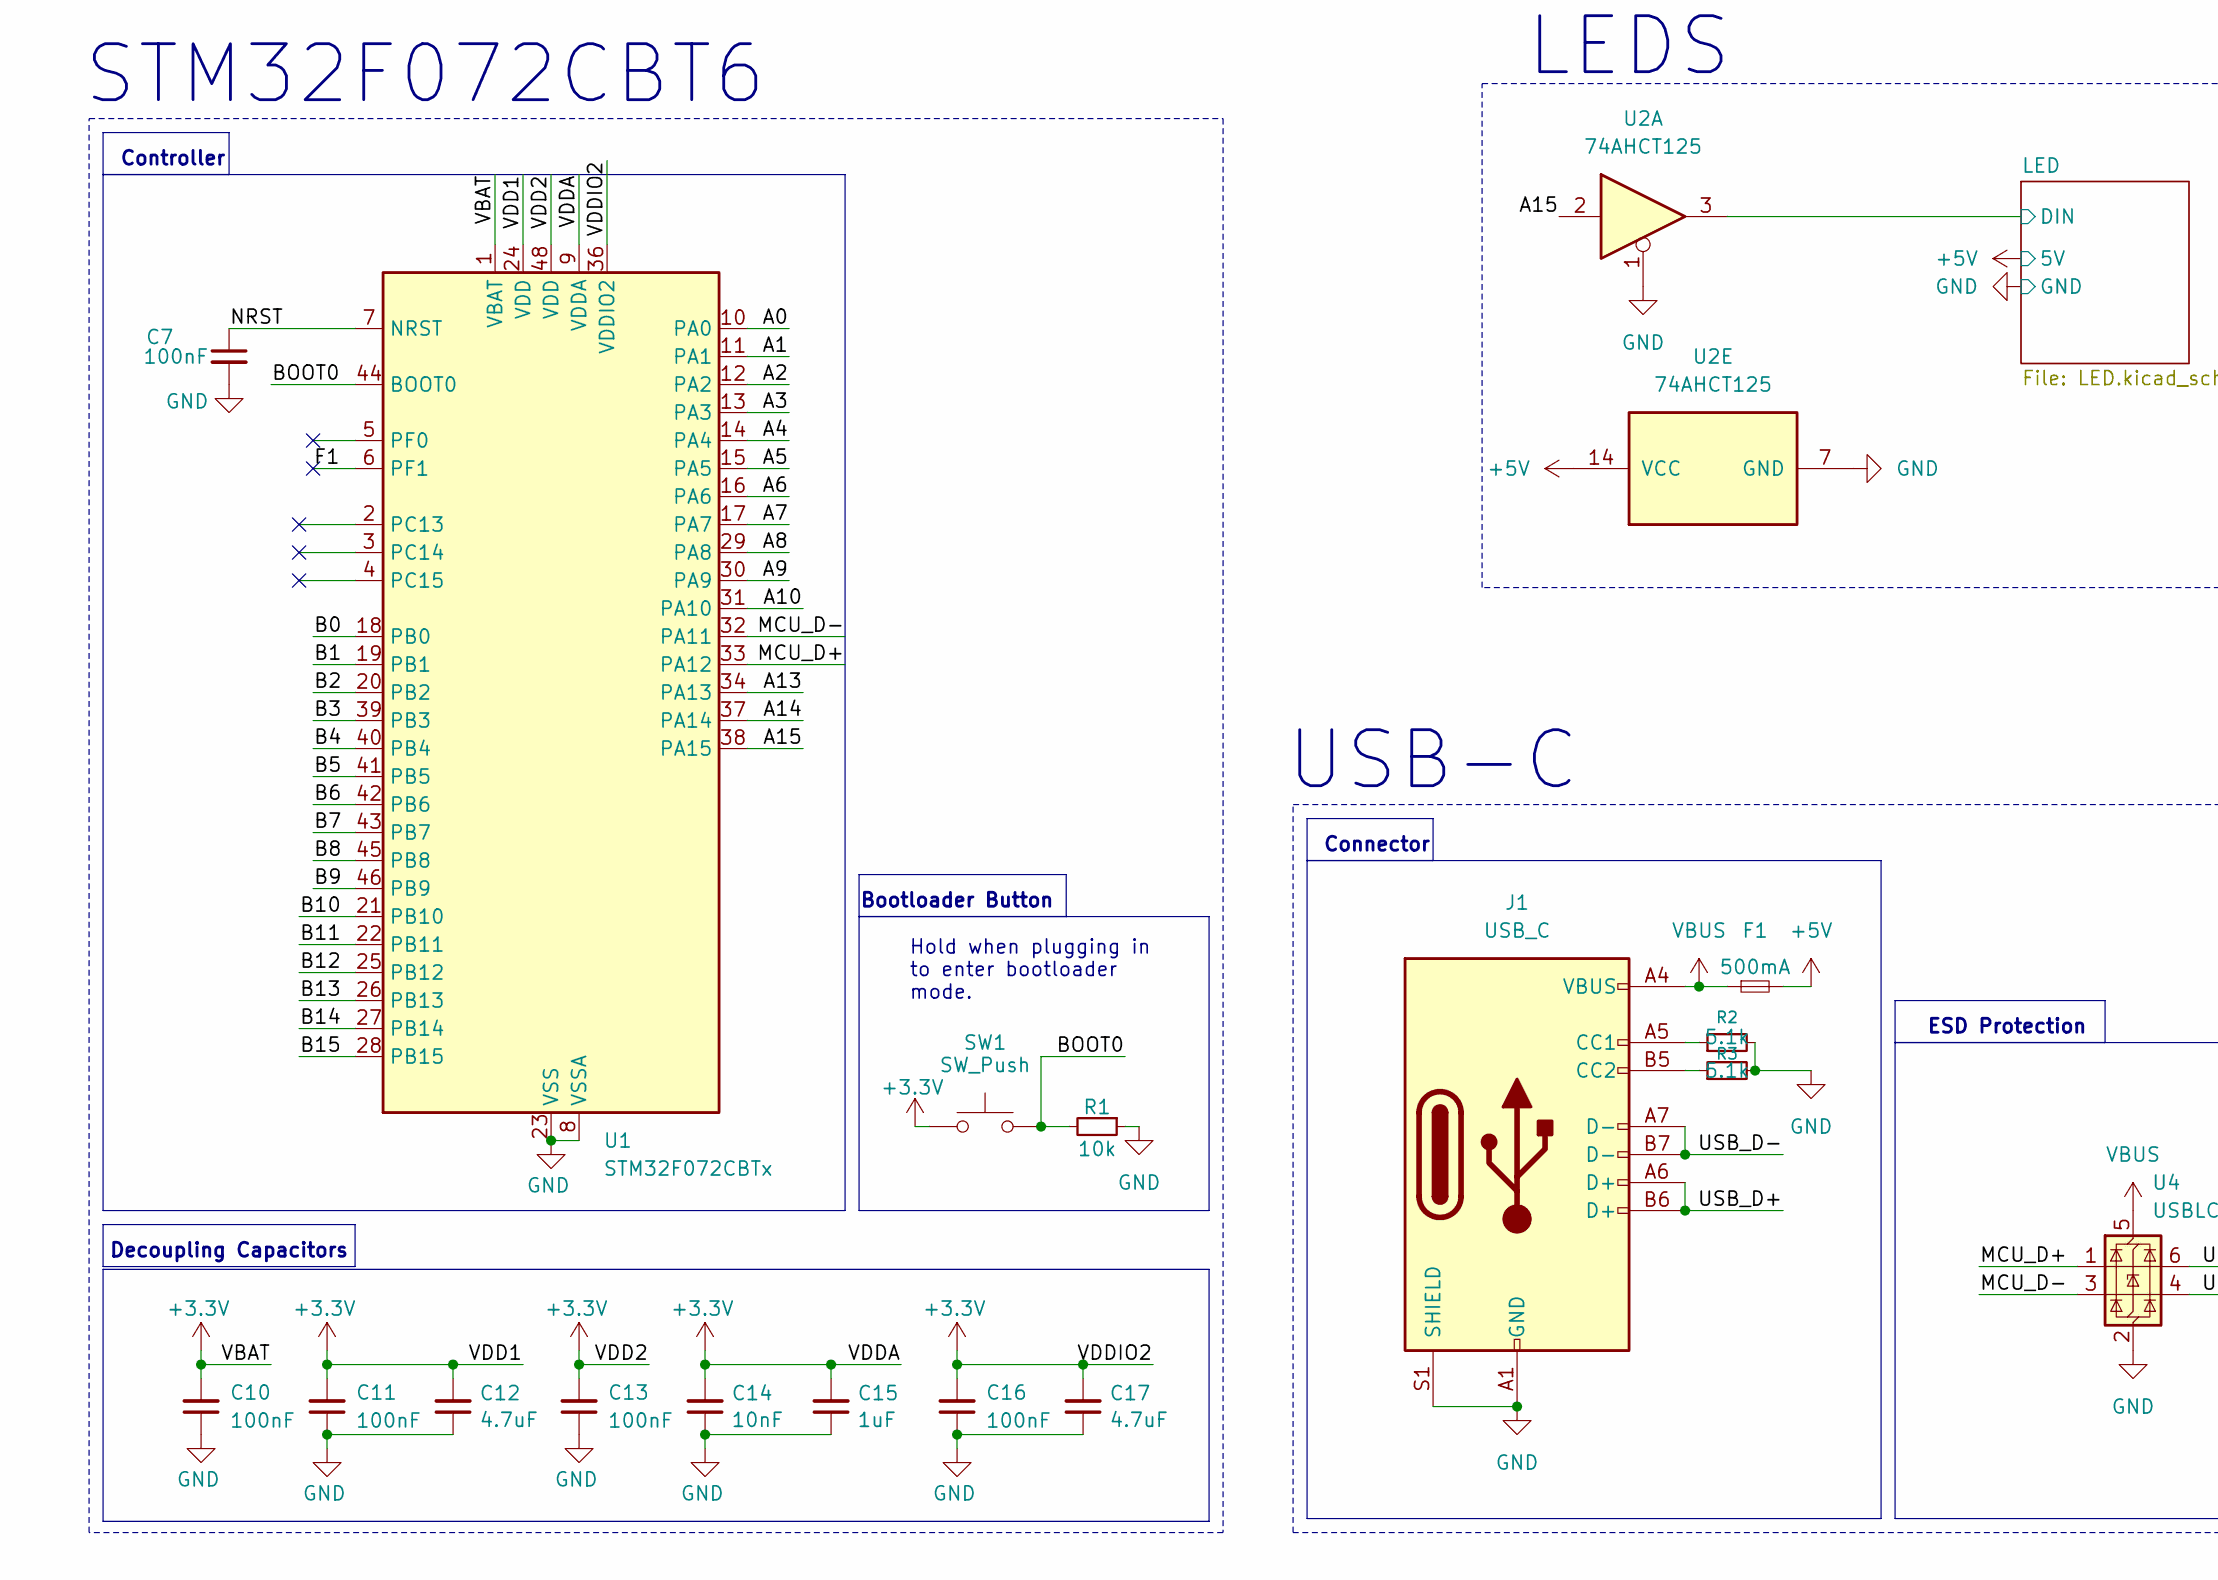
[picture p6: schematic ScottoModules.kicad_sch, part in row 2, column 1]

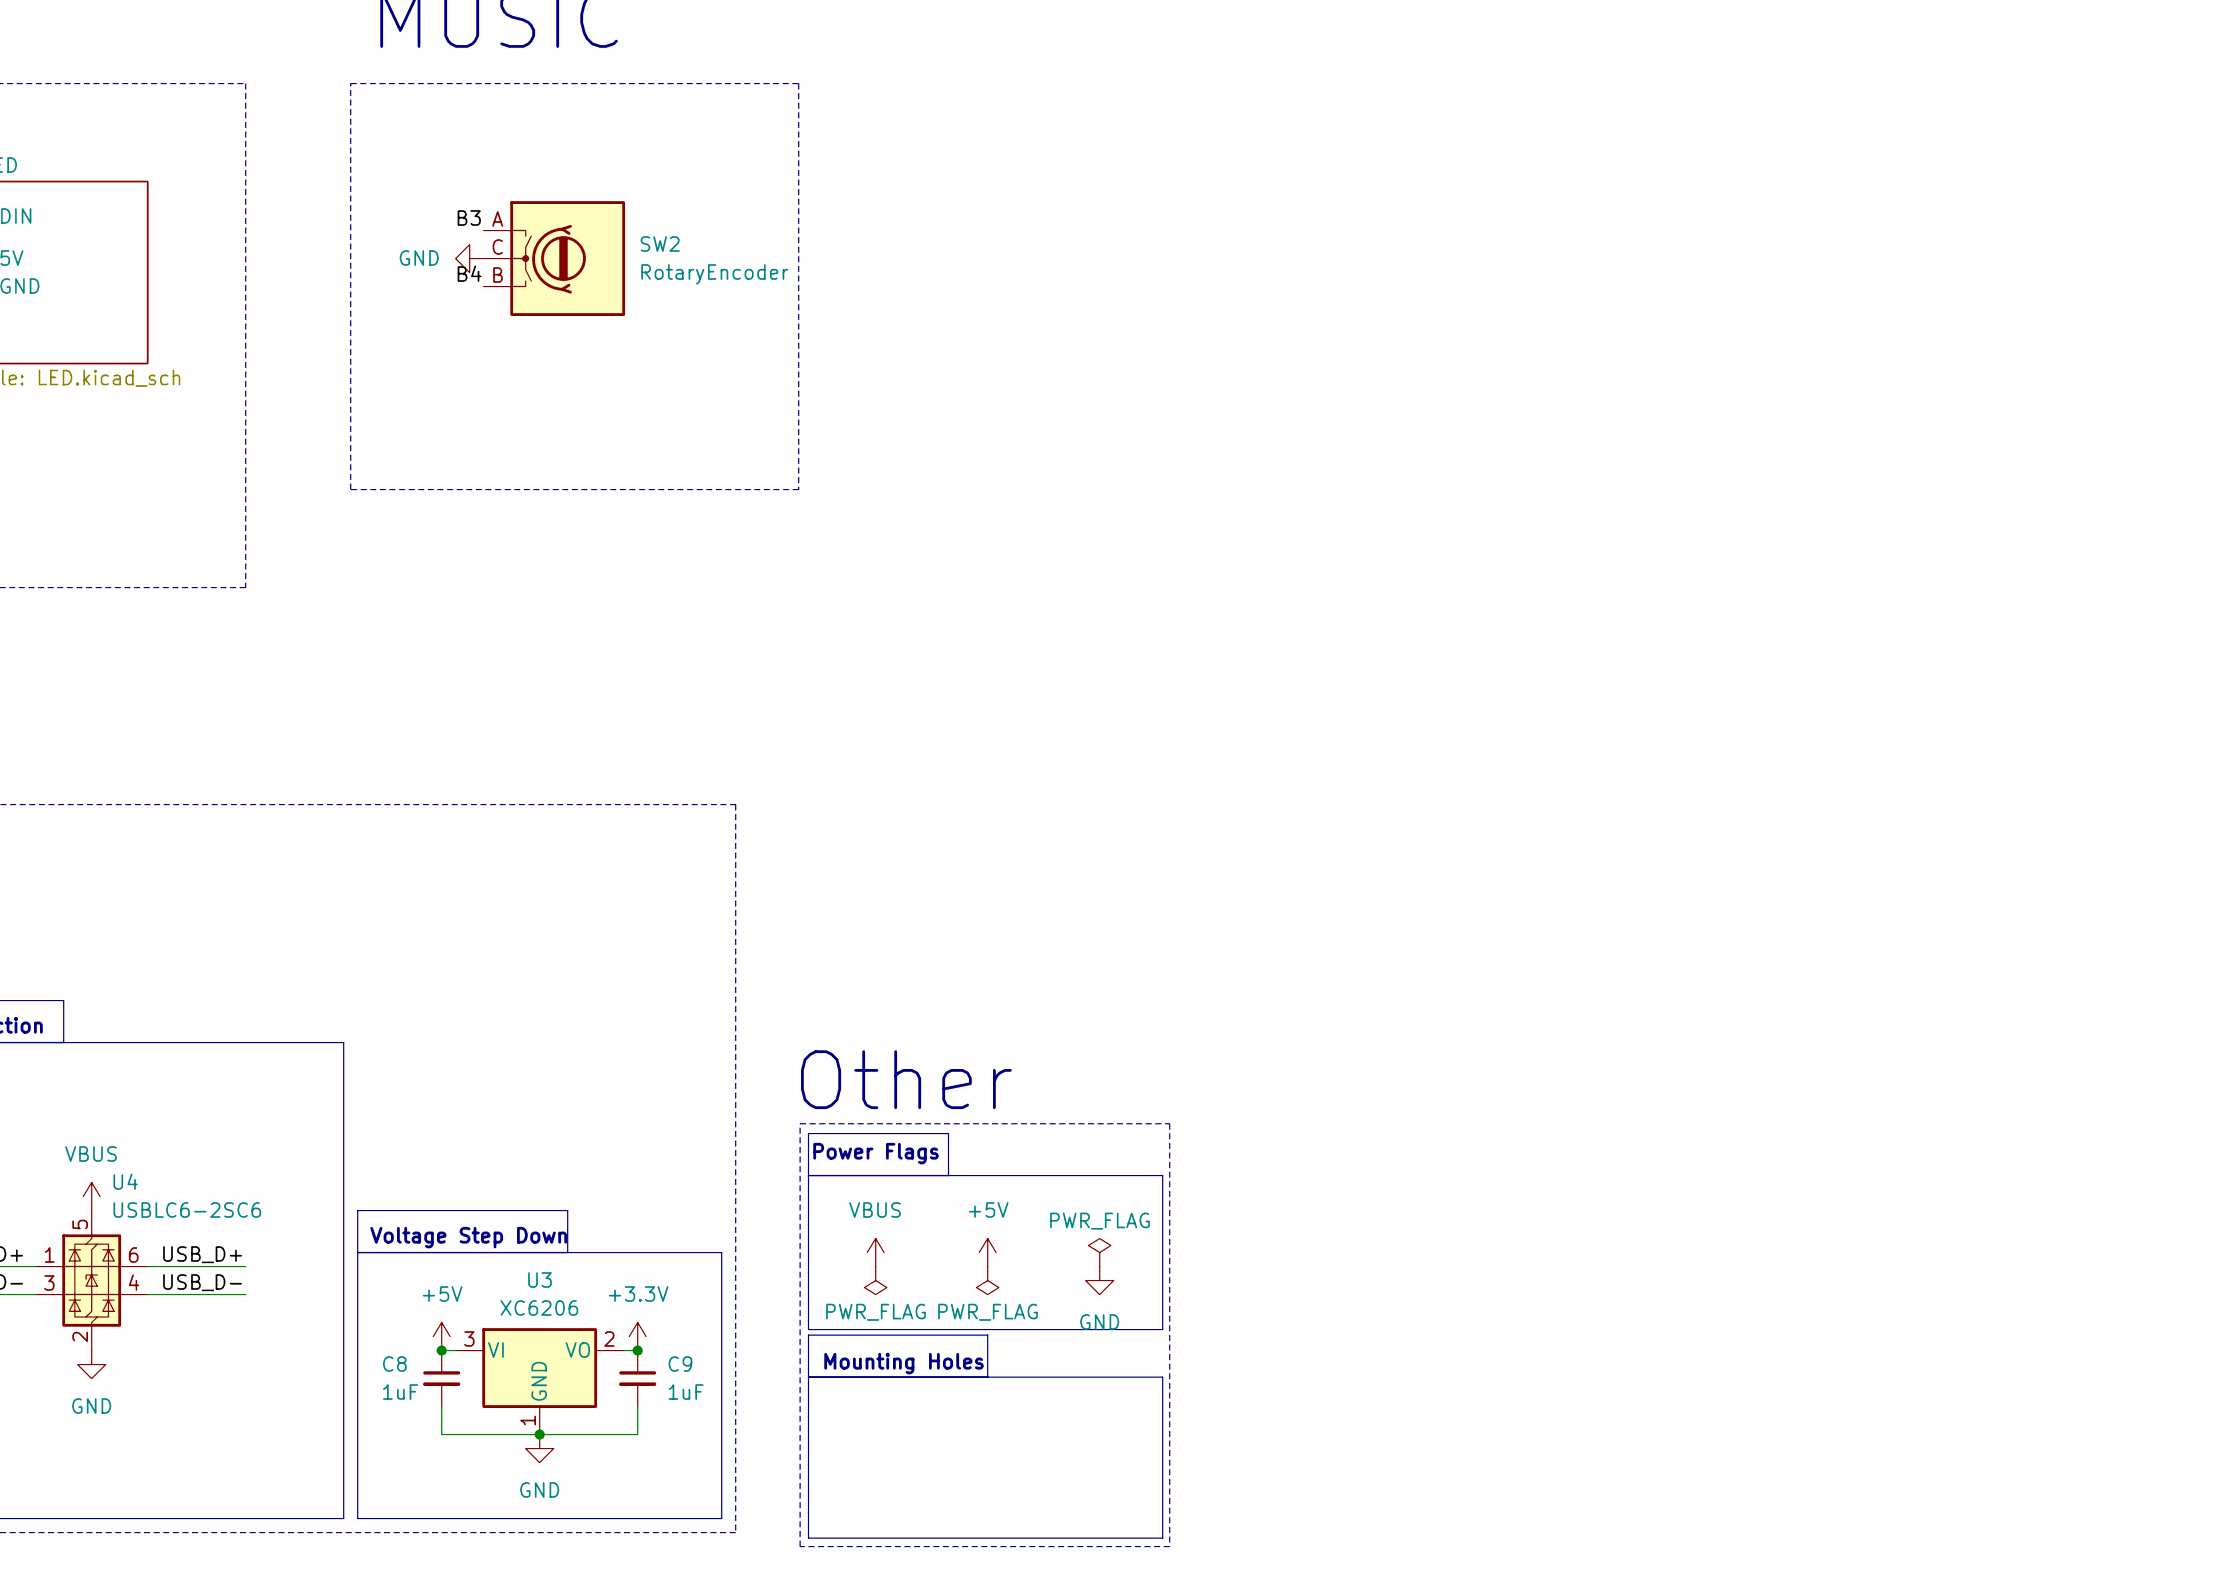
[picture p7: schematic ScottoModules.kicad_sch, part in row 2, column 2]

Parts:
C7: 100nF; Capacitor_0402; LCSC C307331
C8, C9: 1uF; Capacitor_0402; LCSC C52923
C10, C11, C13, C16: 100nF; Capacitor_0402; MPN CL05B104KB54PNC; LCSC C307331
C12, C17: 4.7uF; Capacitor_0402; MPN CL05A475MP5NRNC; LCSC C23733
C14: 10nF; Capacitor_0402; MPN CL05B103KB5NNNC; LCSC C15195
C15: 1uF; Capacitor_0402; MPN CL05A105KA5NQNC; LCSC C52923
D1, D2, D3, D4, D5, D6, D7, D8, D9, D10, D11, D12, D13, D14, D15, D16, D17, D18, D19, D20, D21, D22, D23, D24, D25, D26, D27, D28, D29, D30, D31, D32, D33, D34, D35, D36, D37, D38, D39, D40, D41, D42, D43, D44, D45, D46, D47, D48, D49, D50, D51, D52, D53, D54, D55, D56, D57, D58, D59, D60, D61, D62, D63, D64, D65, D66, D67, D68, D69, D70, D71, D72, D73, D74, D75, D76, D77, D78, D79, D80, D81, D82, D83, D84, D85, D86, D87, D88, D89, D90, D91, D92, D93, D94, D95, D96, D97, D98, D99, D100, D101: Diode; Diode_DO-35
F1: 500mA; Fuse_0603; LCSC C210357
J1: USB_C; USB_C_HRO_TYPE-C-31-M-12; LCSC C165948
R1: 10k; Resistor_0402; LCSC C25744
R2, R3: 5.1k; Resistor_0402
S1, S2, S3, S4, S5, S6, S7, S8, S9, S10, S11, S12, S13, S14, S15, S16, S17, S18, S19, S20, S21, S22, S23, S24, S25, S26, S27, S28, S29, S30, S31, S32, S33, S34, S35, S36, S37, S38, S39, S40, S41, S42, S43, S44, S45, S46, S47, S48, S49, S50, S51, S52, S53, S54, S55, S56, S57, S58, S59, S60, S61, S62, S63, S64, S65, S66, S67, S68, S69, S70, S71, S72, S73, S74, S75, S76, S77, S78, S79, S80, S81, S82, S83, S84, S85, S86, S87, S88, S89, S90, S91, S92, S93, S94, S95, S96, S97, S98, S99, S100, S101: Keyswitch; Hotswap_MX_1.00u
SW1: SW_Push; Button_TL3342; LCSC C115351
SW2: RotaryEncoder; RotaryEncoder_Alps_EC11E_Vertical_H20mm
U1: STM32F072CBTx; LQFP-48_7x7mm_P0.5mm
U2: 74AHCT125; DIP-14_W7.62mm
U3: XC6206; Voltage_SOT-23; LCSC C5446
U4: USBLC6-2SC6; ESD_SOT-23-6; LCSC C2827654

Connections:
+3.3V: C9.1, C10.2, C11.2, C12.2, C13.2, C14.2, C15.2, C16.2, C17.2, SW1.1, U1.1 (VBAT), U1.9 (VDDA), U1.24 (VDD), U1.36 (VDDIO2), U1.48 (VDD), U3.2 (VO)
+5V: C8.1, F1.2, U2.14 (VCC), U3.3 (VI)
A0: S34.1, S55.1, S88.1, U1.10 (PA0)
A1: S33.1, S54.1, S71.1, S87.1, S101.1, U1.11 (PA1)
A2: S32.1, S53.1, S70.1, S86.1, U1.12 (PA2)
A3: S31.1, S52.1, S69.1, S85.1, S100.1, U1.13 (PA3)
A4: S30.1, S51.1, S99.1, U1.14 (PA4)
A5: S29.1, S50.1, S84.1, S98.1, U1.15 (PA5)
A6: S28.1, S49.1, S97.1, U1.16 (PA6)
A7: S27.1, S48.1, S68.1, S83.1, S96.1, U1.17 (PA7)
A8: S4.1, S17.1, S38.1, S59.1, S74.1, S91.1, U1.29 (PA8)
A9: S3.1, S16.1, S37.1, S58.1, S73.1, S90.1, U1.30 (PA9)
A10: S2.1, S15.1, S36.1, S57.1, U1.31 (PA10)
A13: S1.1, S14.1, S35.1, S56.1, S72.1, S89.1, U1.34 (PA13)
A14: D1.1 (K), D2.1 (K), D3.1 (K), D4.1 (K), D5.1 (K), D6.1 (K), D7.1 (K), D8.1 (K), D9.1 (K), D10.1 (K), D11.1 (K), D12.1 (K), D13.1 (K), U1.37 (PA14)
A15: U1.38 (PA15), U2.2
B0: S13.1, S26.1, S47.1, S95.1, U1.18 (PB0)
B1: S12.1, S25.1, S46.1, S67.1, S82.1, S94.1, U1.19 (PB1)
B2: S11.1, S24.1, S45.1, S66.1, S81.1, S93.1, U1.20 (PB2)
B3: SW2.A, U1.39 (PB3)
B4: SW2.B, U1.40 (PB4)
B5: D89.1 (K), D90.1 (K), D91.1 (K), D92.1 (K), D93.1 (K), D94.1 (K), D95.1 (K), D96.1 (K), D97.1 (K), D98.1 (K), D99.1 (K), D100.1 (K), D101.1 (K), U1.41 (PB5)
B6: D72.1 (K), D73.1 (K), D74.1 (K), D75.1 (K), D76.1 (K), D77.1 (K), D78.1 (K), D79.1 (K), D80.1 (K), D81.1 (K), D82.1 (K), D83.1 (K), D84.1 (K), D85.1 (K), D86.1 (K), D87.1 (K), D88.1 (K), U1.42 (PB6)
B7: D56.1 (K), D57.1 (K), D58.1 (K), D59.1 (K), D60.1 (K), D61.1 (K), D62.1 (K), D63.1 (K), D64.1 (K), D65.1 (K), D66.1 (K), D67.1 (K), D68.1 (K), D69.1 (K), D70.1 (K), D71.1 (K), U1.43 (PB7)
B8: D35.1 (K), D36.1 (K), D37.1 (K), D38.1 (K), D39.1 (K), D40.1 (K), D41.1 (K), D42.1 (K), D43.1 (K), D44.1 (K), D45.1 (K), D46.1 (K), D47.1 (K), D48.1 (K), D49.1 (K), D50.1 (K), D51.1 (K), D52.1 (K), D53.1 (K), D54.1 (K), D55.1 (K), U1.45 (PB8)
B9: D14.1 (K), D15.1 (K), D16.1 (K), D17.1 (K), D18.1 (K), D19.1 (K), D20.1 (K), D21.1 (K), D22.1 (K), D23.1 (K), D24.1 (K), D25.1 (K), D26.1 (K), D27.1 (K), D28.1 (K), D29.1 (K), D30.1 (K), D31.1 (K), D32.1 (K), D33.1 (K), D34.1 (K), U1.46 (PB9)
B10: S10.1, S23.1, S44.1, S65.1, S80.1, U1.21 (PB10)
B11: S9.1, S22.1, S43.1, S64.1, S79.1, U1.22 (PB11)
B12: S8.1, S21.1, S42.1, S63.1, S78.1, U1.25 (PB12)
B13: S7.1, S20.1, S41.1, S62.1, S77.1, S92.1, U1.26 (PB13)
B14: S6.1, S19.1, S40.1, S61.1, S76.1, U1.27 (PB14)
B15: S5.1, S18.1, S39.1, S60.1, S75.1, U1.28 (PB15)
BOOT0: R1.2, SW1.2, U1.44 (BOOT0)
DIN: U2.3
F1: U1.6 (PF1)
GND: C7.2, C8.2, C9.2, C10.1, C11.1, C12.1, C13.1, C14.1, C15.1, C16.1, C17.1, J1.A1 (GND), J1.A12 (GND), J1.B1 (GND), J1.B12 (GND), J1.S1 (SHIELD), R1.1, R2.2, R3.2, SW2.C, U1.8 (VSSA), U1.23 (VSS), U1.35 (VSS), U1.47 (VSS), U2.1, U2.7 (GND), U3.1 (GND), U4.2 (GND)
MCU_D+: U1.33 (PA12), U4.1 (I/O1)
MCU_D-: U1.32 (PA11), U4.3 (I/O2)
NRST: C7.1, U1.7 (NRST)
unnamed: D1.2 (A), S1.2
unnamed: D2.2 (A), S2.2
unnamed: D3.2 (A), S3.2
unnamed: D4.2 (A), S4.2
unnamed: D5.2 (A), S5.2
unnamed: D6.2 (A), S6.2
unnamed: D7.2 (A), S7.2
unnamed: D8.2 (A), S8.2
unnamed: D9.2 (A), S9.2
unnamed: D10.2 (A), S10.2
unnamed: D11.2 (A), S11.2
unnamed: D12.2 (A), S12.2
unnamed: D13.2 (A), S13.2
unnamed: D14.2 (A), S14.2
unnamed: D15.2 (A), S15.2
unnamed: D16.2 (A), S16.2
unnamed: D17.2 (A), S17.2
unnamed: D18.2 (A), S18.2
unnamed: D19.2 (A), S19.2
unnamed: D20.2 (A), S20.2
unnamed: D21.2 (A), S21.2
unnamed: D22.2 (A), S22.2
unnamed: D23.2 (A), S23.2
unnamed: D24.2 (A), S24.2
unnamed: D25.2 (A), S25.2
unnamed: D26.2 (A), S26.2
unnamed: D27.2 (A), S27.2
unnamed: D28.2 (A), S28.2
unnamed: D29.2 (A), S29.2
unnamed: D30.2 (A), S30.2
unnamed: D31.2 (A), S31.2
unnamed: D32.2 (A), S32.2
unnamed: D33.2 (A), S33.2
unnamed: D34.2 (A), S34.2
unnamed: D35.2 (A), S35.2
unnamed: D36.2 (A), S36.2
unnamed: D37.2 (A), S37.2
unnamed: D38.2 (A), S38.2
unnamed: D39.2 (A), S39.2
unnamed: D40.2 (A), S40.2
unnamed: D41.2 (A), S41.2
unnamed: D42.2 (A), S42.2
unnamed: D43.2 (A), S43.2
unnamed: D44.2 (A), S44.2
unnamed: D45.2 (A), S45.2
unnamed: D46.2 (A), S46.2
unnamed: D47.2 (A), S47.2
unnamed: D48.2 (A), S48.2
unnamed: D49.2 (A), S49.2
unnamed: D50.2 (A), S50.2
unnamed: D51.2 (A), S51.2
unnamed: D52.2 (A), S52.2
unnamed: D53.2 (A), S53.2
unnamed: D54.2 (A), S54.2
unnamed: D55.2 (A), S55.2
unnamed: D56.2 (A), S56.2
unnamed: D57.2 (A), S57.2
unnamed: D58.2 (A), S58.2
unnamed: D59.2 (A), S59.2
unnamed: D60.2 (A), S60.2
unnamed: D61.2 (A), S61.2
unnamed: D62.2 (A), S62.2
unnamed: D63.2 (A), S63.2
unnamed: D64.2 (A), S64.2
unnamed: D65.2 (A), S65.2
unnamed: D66.2 (A), S66.2
unnamed: D67.2 (A), S67.2
unnamed: D68.2 (A), S68.2
unnamed: D69.2 (A), S69.2
unnamed: D70.2 (A), S70.2
unnamed: D71.2 (A), S71.2
unnamed: D72.2 (A), S72.2
unnamed: D73.2 (A), S73.2
unnamed: D74.2 (A), S74.2
unnamed: D75.2 (A), S75.2
unnamed: D76.2 (A), S76.2
unnamed: D77.2 (A), S77.2
unnamed: D78.2 (A), S78.2
unnamed: D79.2 (A), S79.2
unnamed: D80.2 (A), S80.2
unnamed: D81.2 (A), S81.2
unnamed: D82.2 (A), S82.2
unnamed: D83.2 (A), S83.2
unnamed: D84.2 (A), S84.2
unnamed: D85.2 (A), S85.2
unnamed: D86.2 (A), S86.2
unnamed: D87.2 (A), S87.2
unnamed: D88.2 (A), S88.2
unnamed: D89.2 (A), S89.2
unnamed: D90.2 (A), S90.2
unnamed: D91.2 (A), S91.2
unnamed: D92.2 (A), S92.2
unnamed: D93.2 (A), S93.2
unnamed: D94.2 (A), S94.2
unnamed: D95.2 (A), S95.2
unnamed: D96.2 (A), S96.2
unnamed: D97.2 (A), S97.2
unnamed: D98.2 (A), S98.2
unnamed: D99.2 (A), S99.2
unnamed: D100.2 (A), S100.2
unnamed: D101.2 (A), S101.2
unnamed: J1.A5 (CC1), R2.1
unnamed: J1.B5 (CC2), R3.1
USB_D+: J1.A6 (D+), J1.B6 (D+), U4.6 (I/O1)
USB_D-: J1.A7 (D-), J1.B7 (D-), U4.4 (I/O2)
VBUS: F1.1, J1.A4 (VBUS), J1.A9 (VBUS), J1.B4 (VBUS), J1.B9 (VBUS), U4.5 (VBUS)

Notes on the sheet:
STM32F072CBT6
USB-C
Mounting Holes
Decoupling Capacitors
MUSIC
Controller
ESD Protection
Power Flags
LEDS
Voltage Step Down
Matrix
Other
Bootloader Button
Connector
Hold when plugging in to enter bootloader mode.
